joshajohnson/rf-sig-gen/firmware/rf-sig-gen/Inc/STP08CP05.h

#ifndef STP08CP05_H_
#define STP08CP05_H_

#include <stdint.h>
#include "main.h"
#include "dwt_stm32_delay.h"

uint8_t freqToLed (float frequency);
void rainbow(void);
void kitt(void);
void binary(void);
void stpSpiTx (uint8_t leds);

#endif
